liquidbase/voron-v0/docs/Input Shaping Graphs/beltscomparison_20240730_230938.png

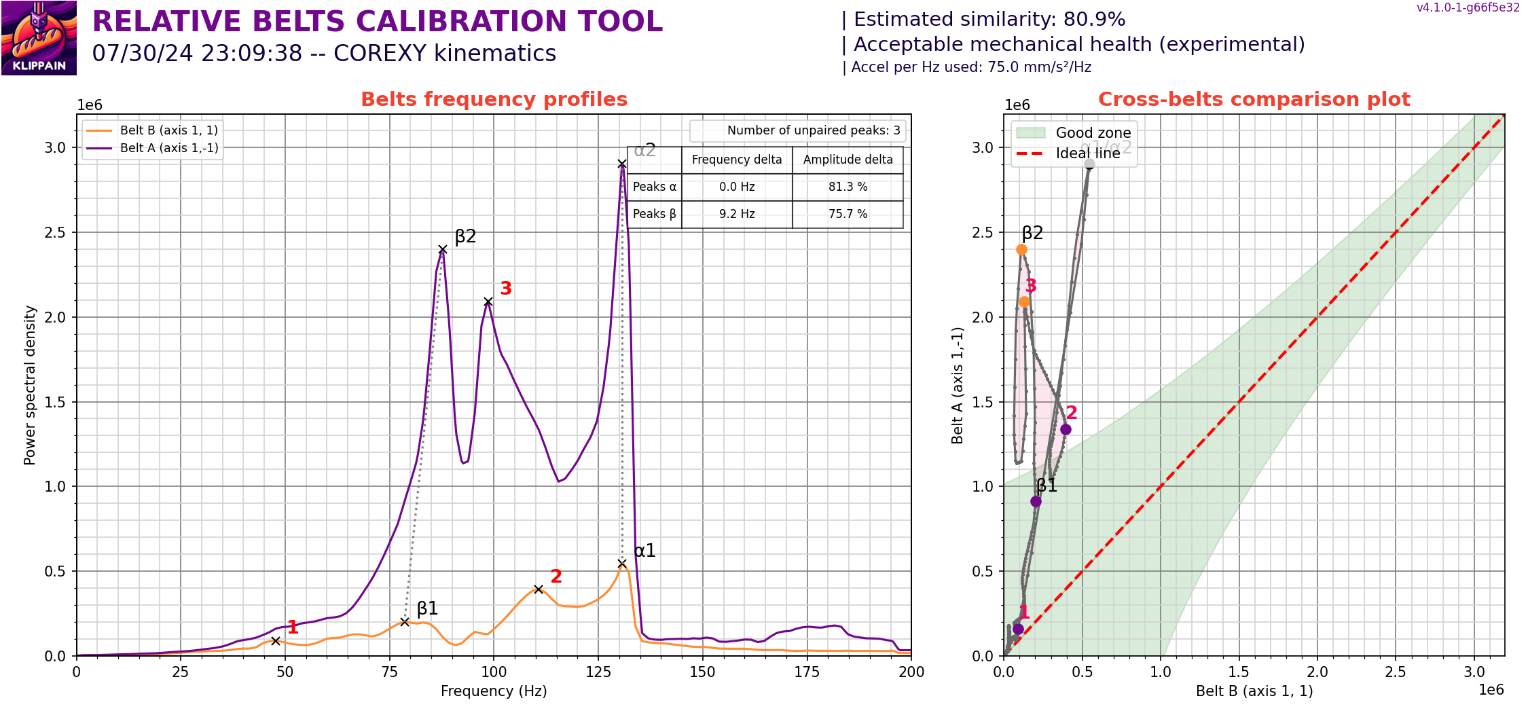
docs/Input Shaping Graphs/beltscomparison_20240730_230938.png
