liquidbase/voron-v0/docs/Input Shaping Graphs/inputshaper_20240730_230241_X.png

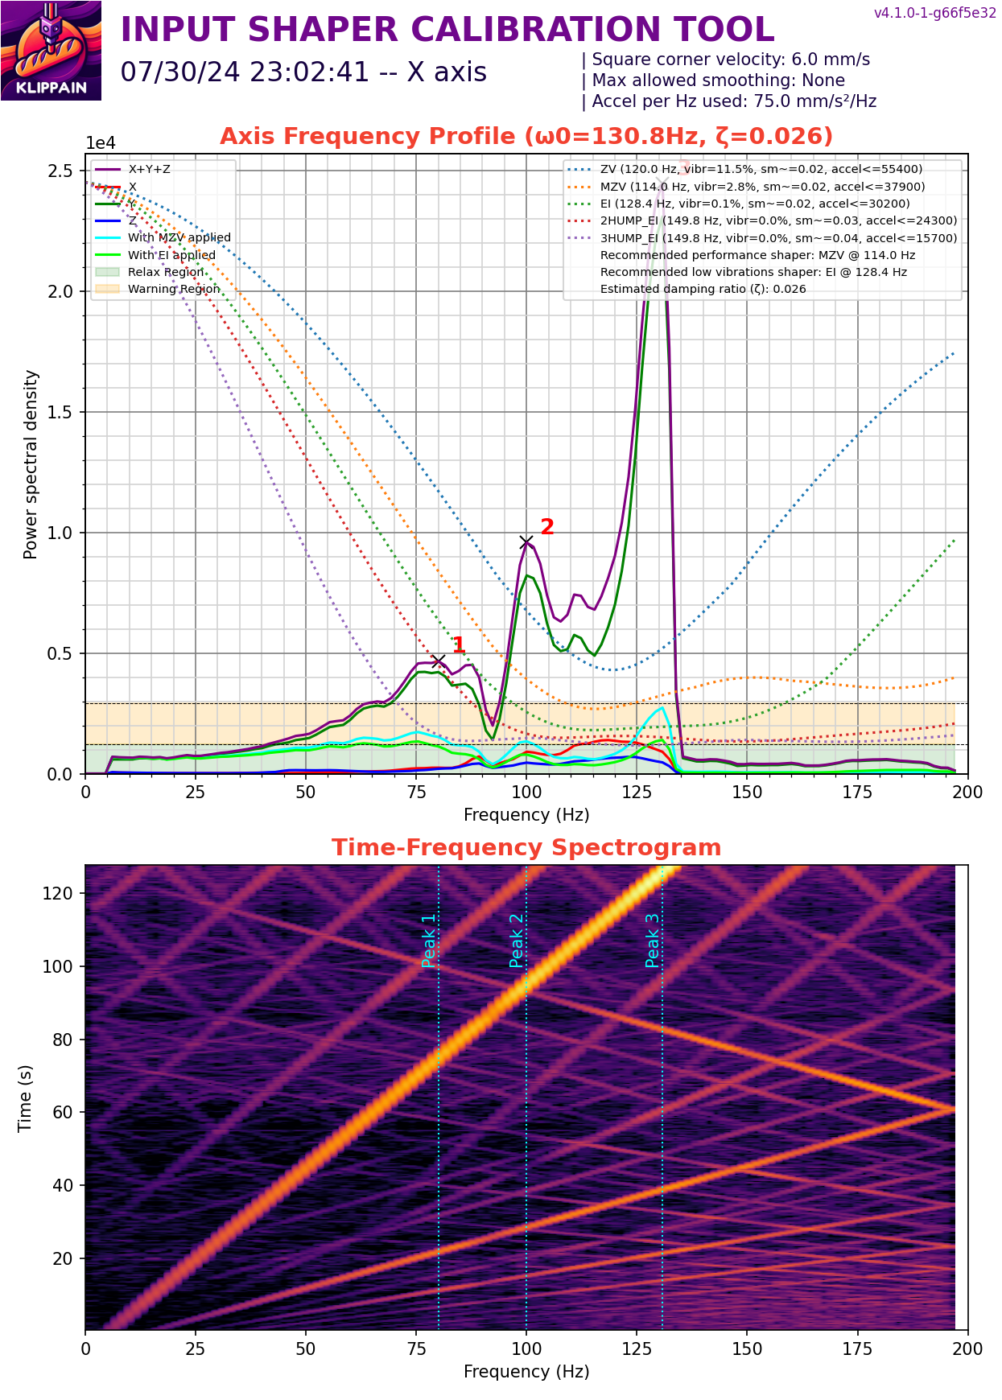
docs/Input Shaping Graphs/inputshaper_20240730_230241_X.png
