liquidbase/voron-v0/docs/Input Shaping Graphs/inputshaper_20240730_233401_Y.png

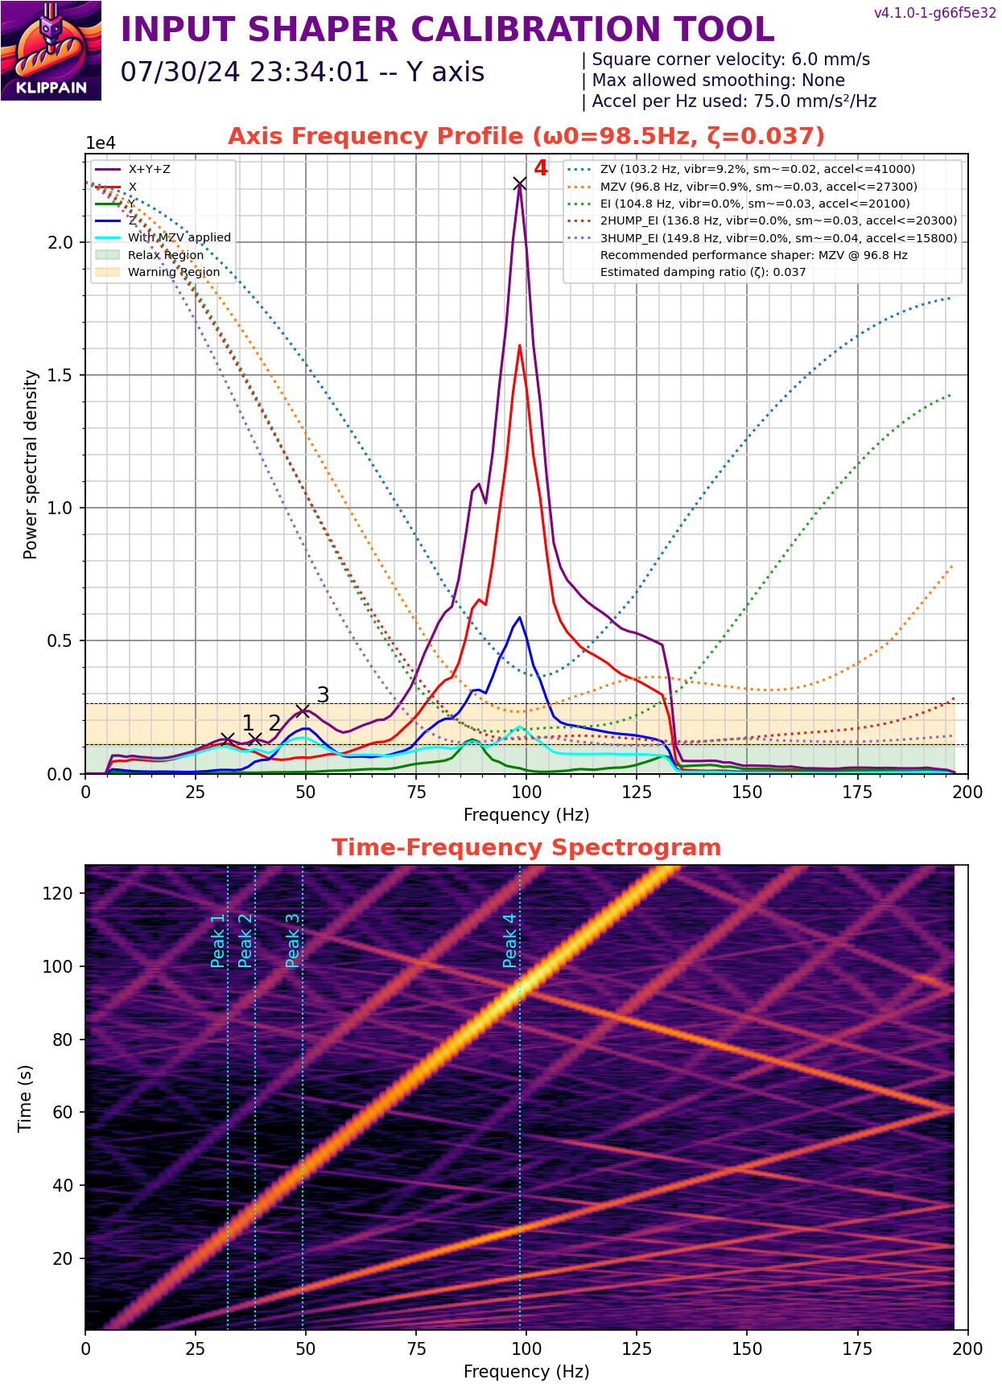
docs/Input Shaping Graphs/inputshaper_20240730_233401_Y.png
