liquidbase/voron-v0/Pictures/extruder_motor.jpg

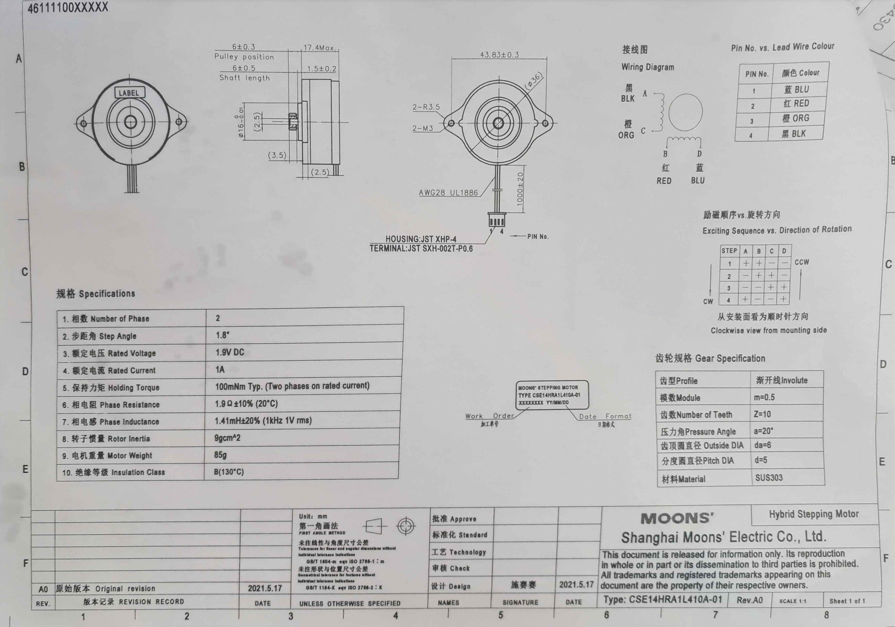
Pictures/extruder_motor.jpg
