liquidbase/voron-v0/Pictures/PXL_20240726_175340386.jpg

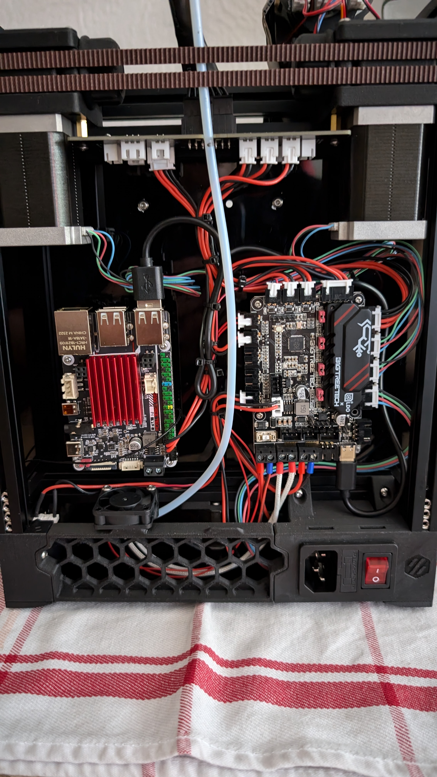
Pictures/PXL_20240726_175340386.jpg
