liquidbase/voron-v0/Pictures/xy_motor.jpg

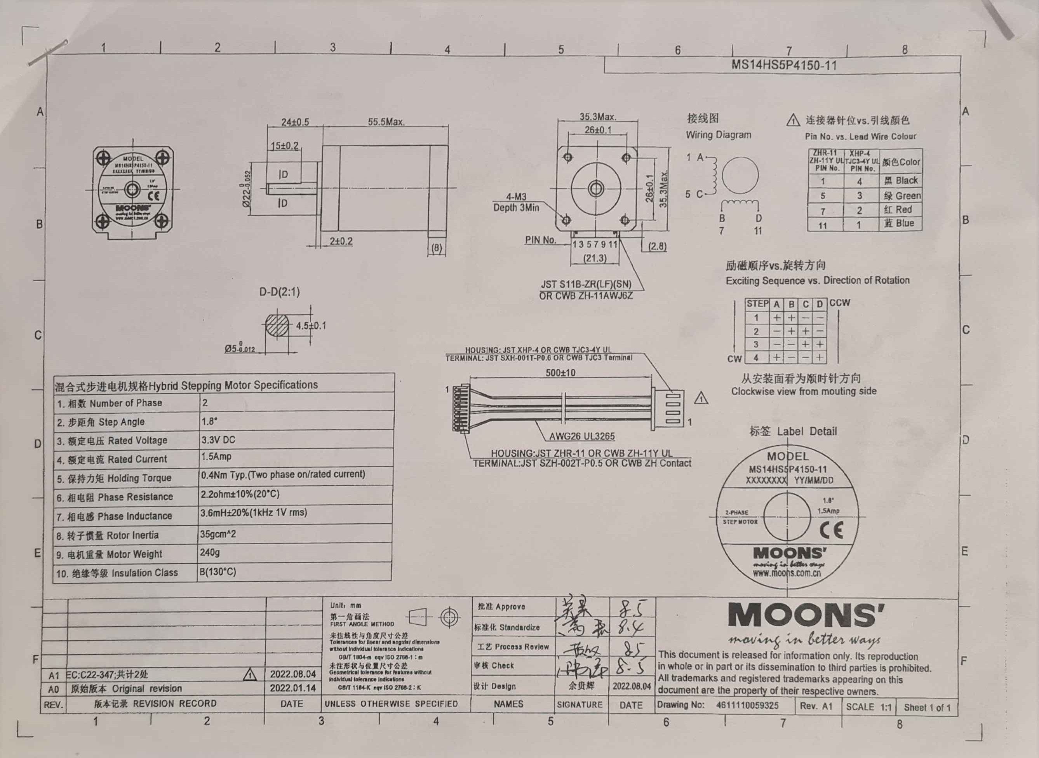
Pictures/xy_motor.jpg
