liquidbase/voron-v0/Pictures/z_motor.jpg

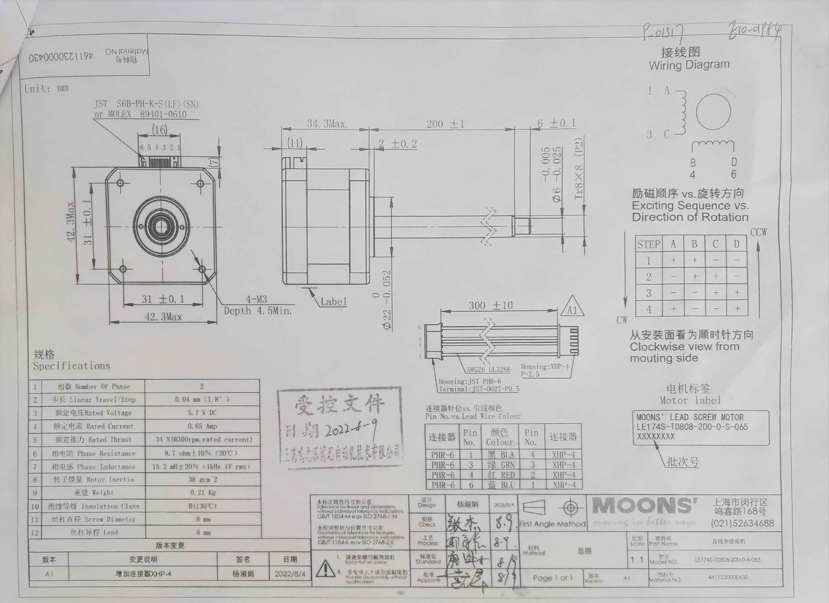
Pictures/z_motor.jpg
