liquidbase/voron-v0/Printfiles/voron-v0-stealth-handles/stealth_handle.step

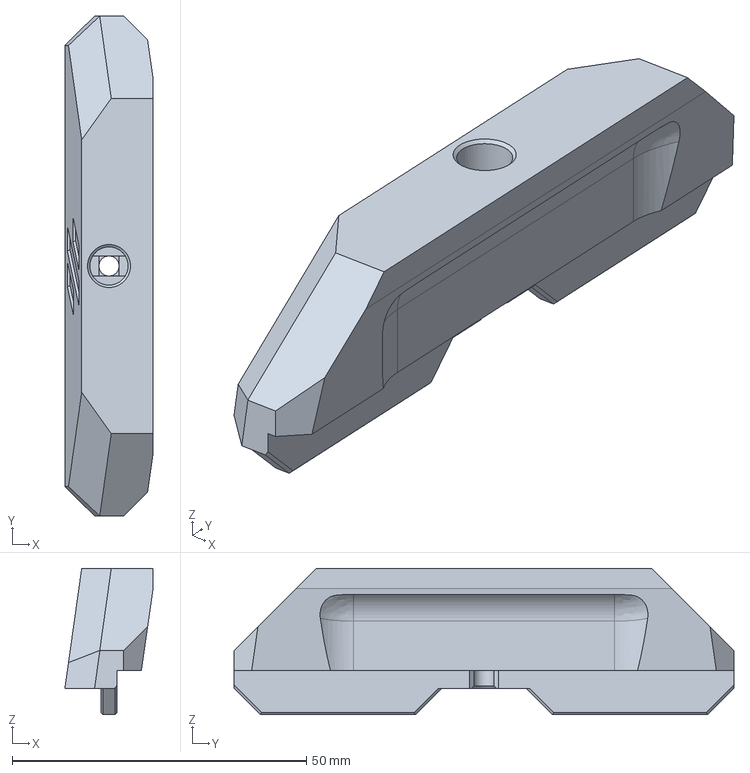
[picture p18: CAD file, 2024-07-29]
Printfiles/voron-v0-stealth-handles/stealth_handle.step
15.0 x 85.0 x 24.9 mm
