liquidbase/voron-v0/Printfiles/Sherpa_Mini-Extruder/Assembly_Tools/Shaft_Grinding_Tool/bottom.stl

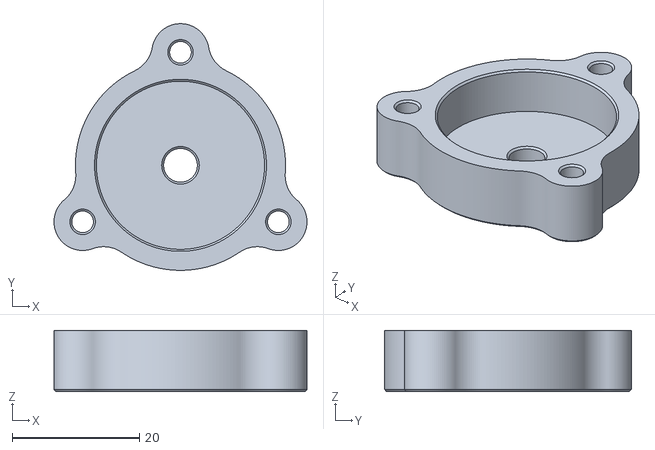
[picture p24: CAD file, 2024-10-22]
Printfiles/Sherpa_Mini-Extruder/Assembly_Tools/Shaft_Grinding_Tool/bottom.stl
39.7 x 38.7 x 9.60
