liquidbase/voron-v0/Printfiles/Sherpa_Mini-Extruder/STLs/housing_rear_x1_rev17.STL

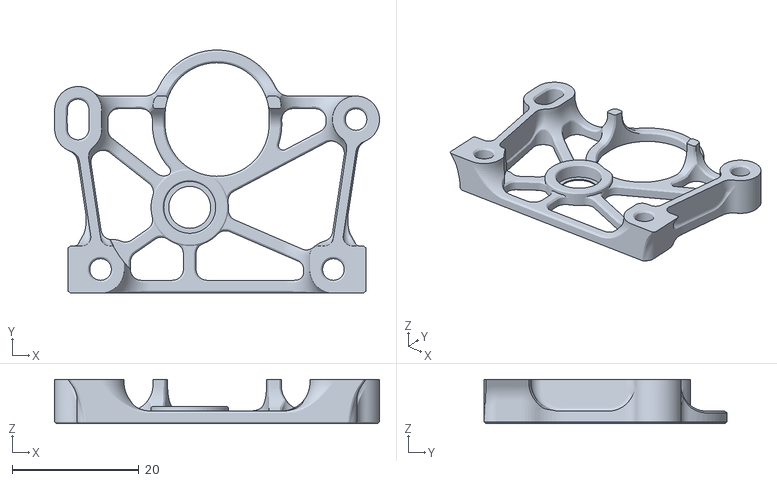
[picture p25: CAD file, 2024-10-22]
Printfiles/Sherpa_Mini-Extruder/STLs/housing_rear_x1_rev17.STL
51.2 x 38.3 x 7.00
