liquidbase/voron-v0/Printfiles/Sherpa_Mini-Extruder/STLs/optional_parts/[a]_housing_front_k_x1_rev15.STL

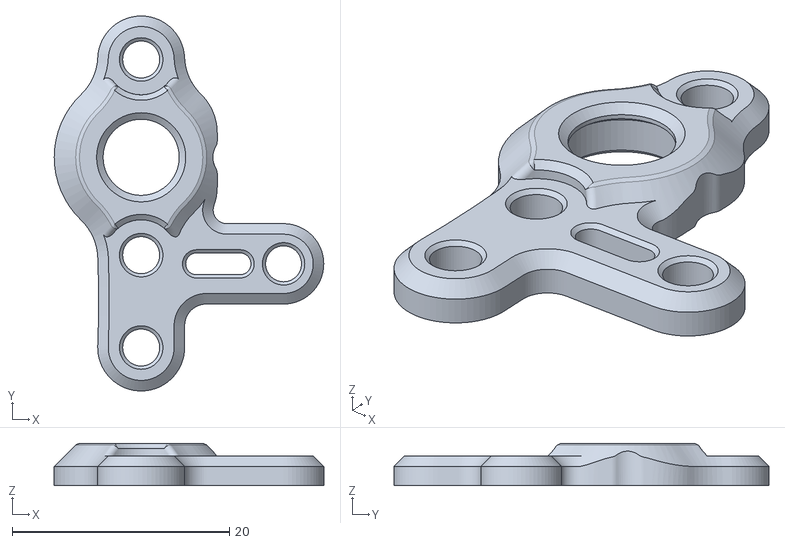
[picture p26: CAD file, 2024-10-22]
Printfiles/Sherpa_Mini-Extruder/STLs/optional_parts/[a]_housing_front_k_x1_rev15.STL
24.8 x 34.5 x 3.90
