liquidbase/voron-v0/Printfiles/voron-v0-stealth-handles/handle_a.stl

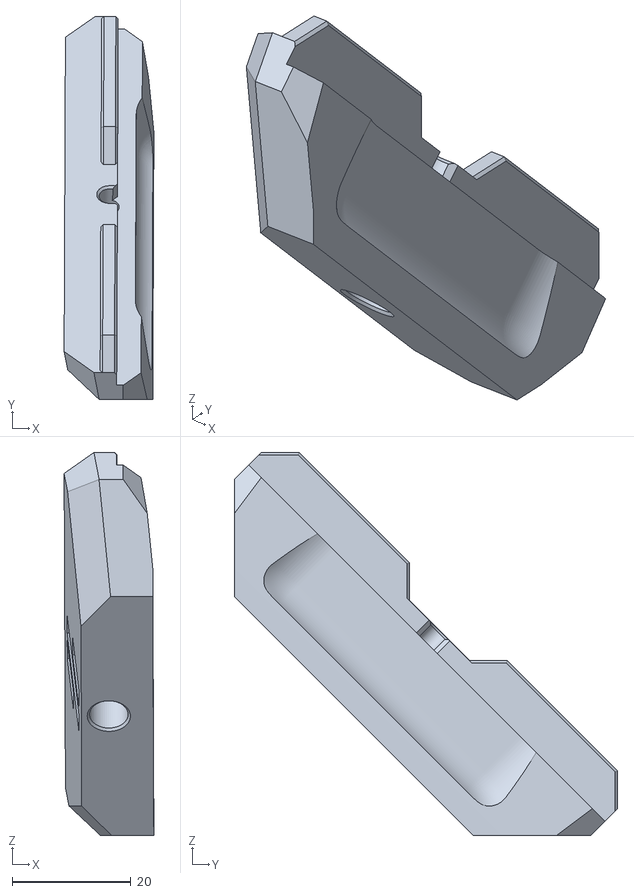
[picture p27: CAD file, 2024-07-29]
Printfiles/voron-v0-stealth-handles/handle_a.stl
15.2 x 64.7 x 64.6
