liquidbase/voron-v0/Printfiles/waveshare-43-inch-display-mount-for-the-voron-v01-model_files/vorn_v0_waveshare_43.3mf

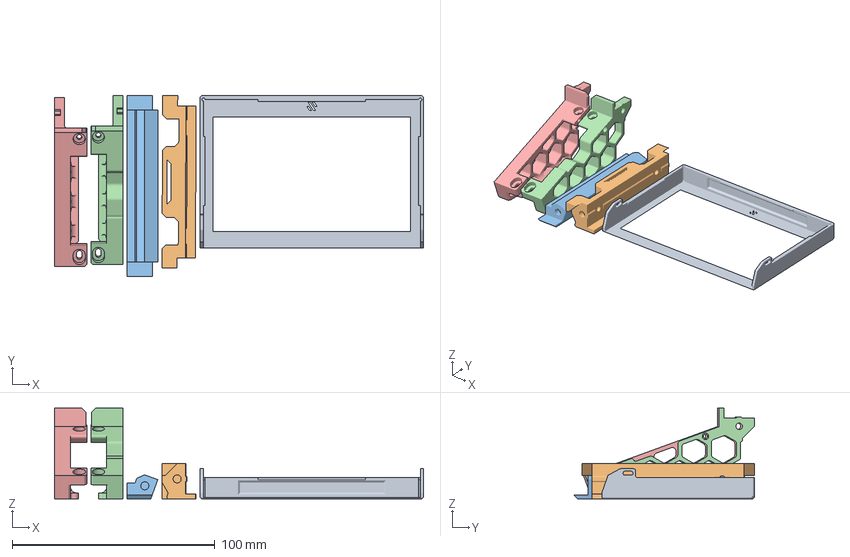
[picture p28: CAD file, 2024-08-06]
Printfiles/waveshare-43-inch-display-mount-for-the-voron-v01-model_files/vorn_v0_waveshare_43.3mf
181.8 x 89.1 x 44.8 mm
cover_front.stl
mount_rear.stl
mount_front.stl
mount_left.stl
mount_right.stl
