liquidbase/voron-v0/Printfiles/[a]_Foot_Accent_A_x2.stl

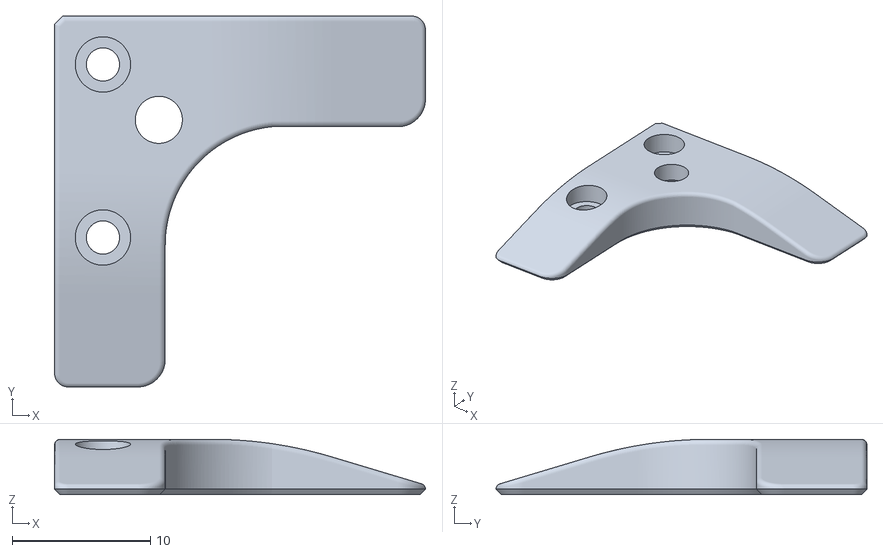
[picture p29: CAD file, 2024-11-05]
Printfiles/[a]_Foot_Accent_A_x2.stl
26.8 x 26.8 x 4.00
