liquidbase/voron-v0/Printfiles/Dragon_Burner_v8_Sherpa_Mini/Sherpa_Mini_Mount.stl

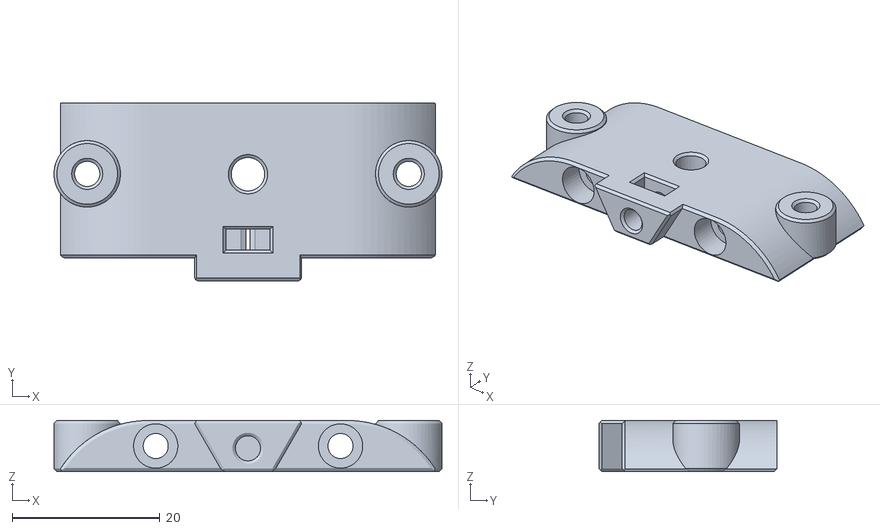
[picture p30: CAD file, 2024-09-15]
Printfiles/Dragon_Burner_v8_Sherpa_Mini/Sherpa_Mini_Mount.stl
52.5 x 24.1 x 6.90
