liquidbase/voron-v0/Printfiles/Endstop Case/1515 Endcap with Endstop Case v14.step

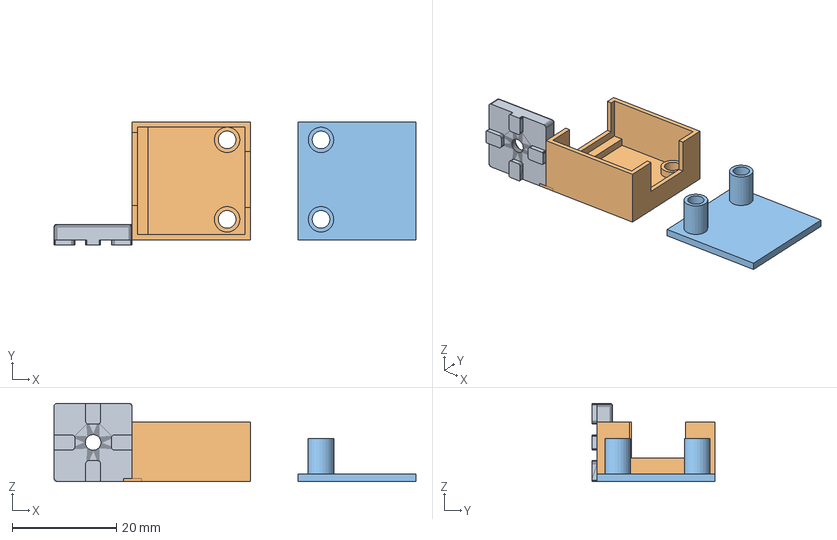
[picture p31: CAD file, 2024-09-08]
Printfiles/Endstop Case/1515 Endcap with Endstop Case v14.step
69.4 x 23.7 x 15.0 mm
