liquidbase/voron-v0/Printfiles/Filler 66mm Remix - 5335512/files/FillerRollerSource-66mm.stl

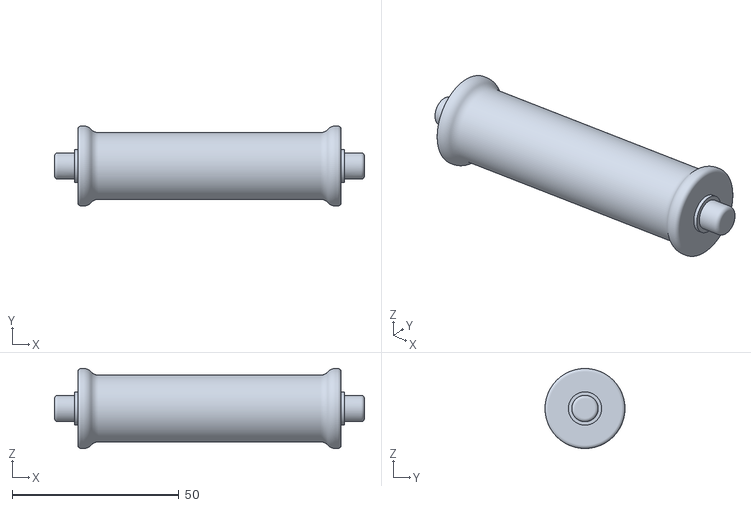
[picture p32: CAD file, 2024-10-22]
Printfiles/Filler 66mm Remix - 5335512/files/FillerRollerSource-66mm.stl
93.0 x 24.0 x 24.0
