liquidbase/voron-v0/Printfiles/Sherpa_Mini-Extruder/Assembly_Tools/Shaft_Grinding_Tool/top.stl

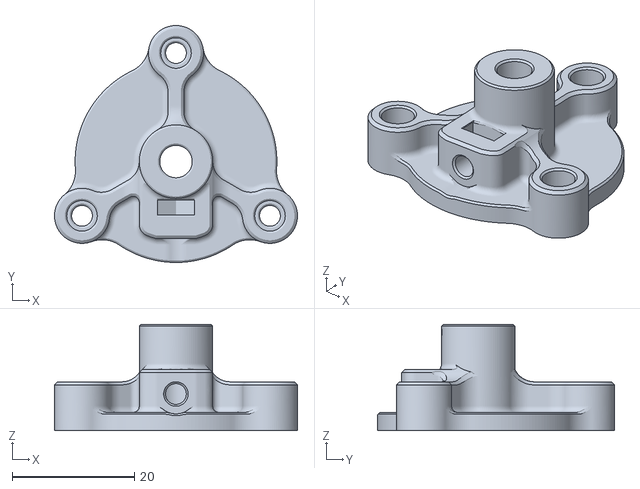
[picture p33: CAD file, 2024-10-22]
Printfiles/Sherpa_Mini-Extruder/Assembly_Tools/Shaft_Grinding_Tool/top.stl
39.7 x 38.8 x 17.4
