liquidbase/voron-v0/Printfiles/Sherpa_Mini-Extruder/STLs/[a]_idler_arm_long_x1_rev16a.STL

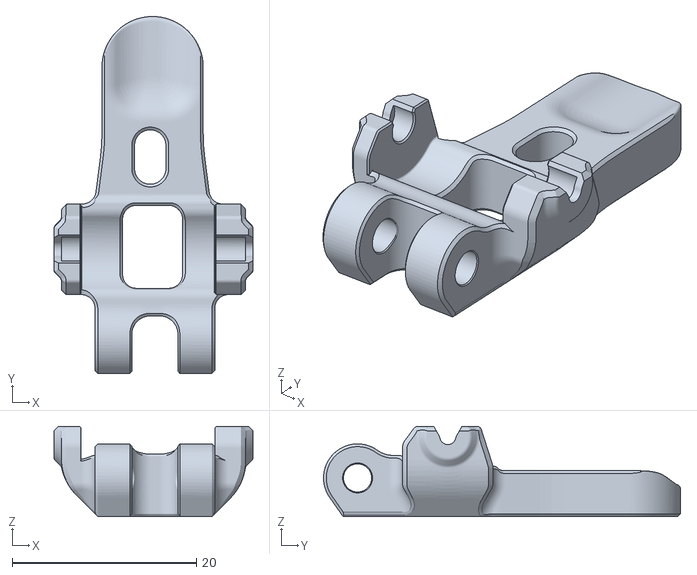
[picture p34: CAD file, 2024-10-22]
Printfiles/Sherpa_Mini-Extruder/STLs/[a]_idler_arm_long_x1_rev16a.STL
21.6 x 38.8 x 9.80
