liquidbase/voron-v0/Printfiles/Sherpa_Mini-Extruder/STLs/optional_parts/[a]_idler_arm_short_x1_rev16a.STL

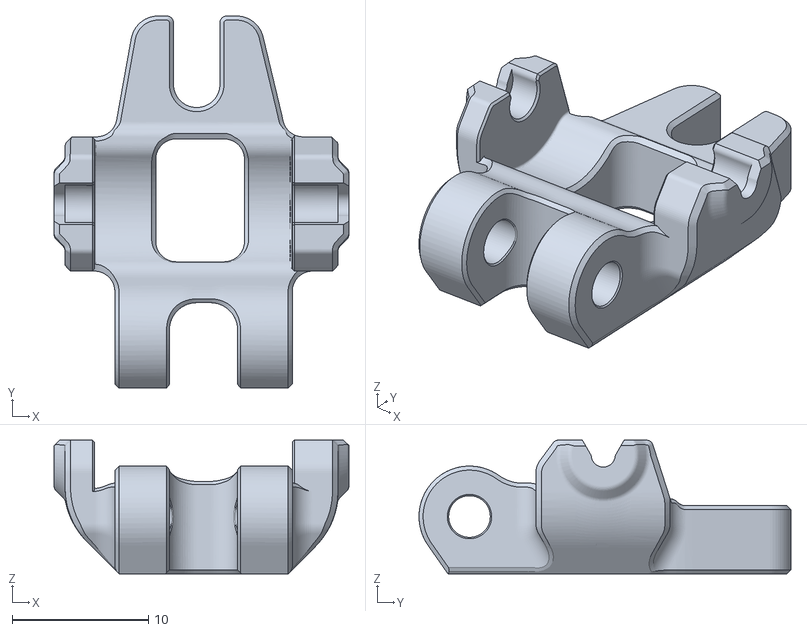
[picture p35: CAD file, 2024-10-22]
Printfiles/Sherpa_Mini-Extruder/STLs/optional_parts/[a]_idler_arm_short_x1_rev16a.STL
21.6 x 27.3 x 9.80
