liquidbase/voron-v0/Printfiles/voron-v0-stealth-handles/handle_b.stl

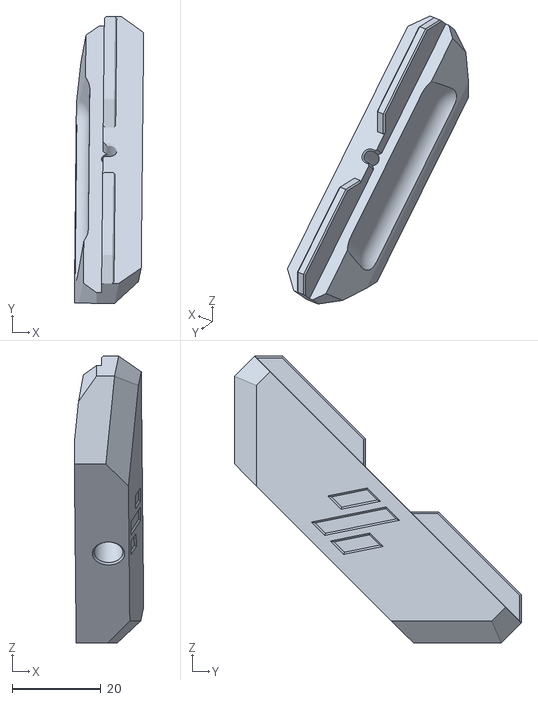
[picture p36: CAD file, 2024-07-29]
Printfiles/voron-v0-stealth-handles/handle_b.stl
15.6 x 64.7 x 64.6
