liquidbase/voron-v0/Printfiles/waveshare-43-inch-display-mount-for-the-voron-v01-model_files/cover_front.stl

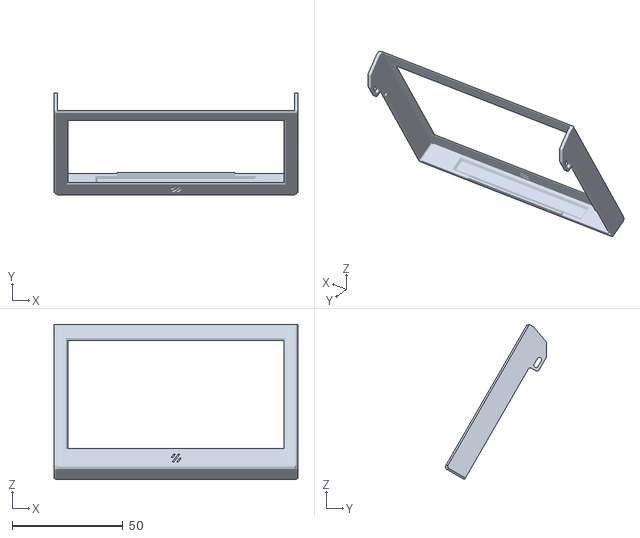
[picture p37: CAD file, 2024-08-06]
Printfiles/waveshare-43-inch-display-mount-for-the-voron-v01-model_files/cover_front.stl
110.0 x 45.8 x 70.0
