liquidbase/voron-v0/Printfiles/Dragon_Burner_v8_Sherpa_Mini/Cowl_ZeroClick.stl

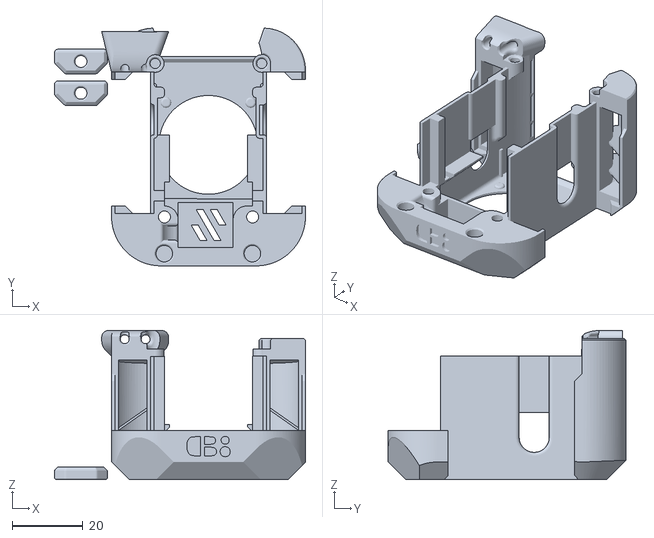
[picture p38: CAD file, 2024-09-14]
Printfiles/Dragon_Burner_v8_Sherpa_Mini/Cowl_ZeroClick.stl
71.2 x 67.4 x 42.4
