liquidbase/voron-v0/Printfiles/waveshare-43-inch-display-mount-for-the-voron-v01-model_files/mount_rear.stl

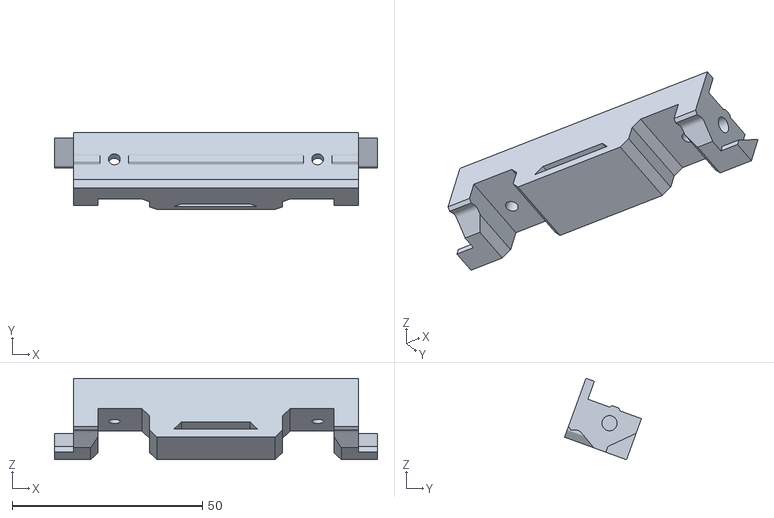
[picture p39: CAD file, 2024-08-06]
Printfiles/waveshare-43-inch-display-mount-for-the-voron-v01-model_files/mount_rear.stl
85.0 x 20.3 x 21.4
