liquidbase/voron-v0/Printfiles/Dragon_Burner_v8_Sherpa_Mini/Brace_Straight.stl

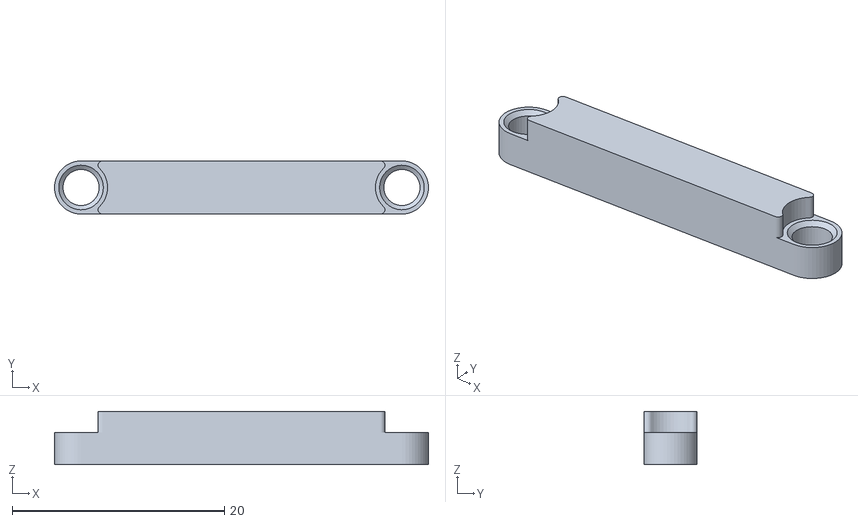
[picture p40: CAD file, 2024-09-14]
Printfiles/Dragon_Burner_v8_Sherpa_Mini/Brace_Straight.stl
35.2 x 5.00 x 5.00
