liquidbase/voron-v0/Printfiles/URBIFS-PC4.stl

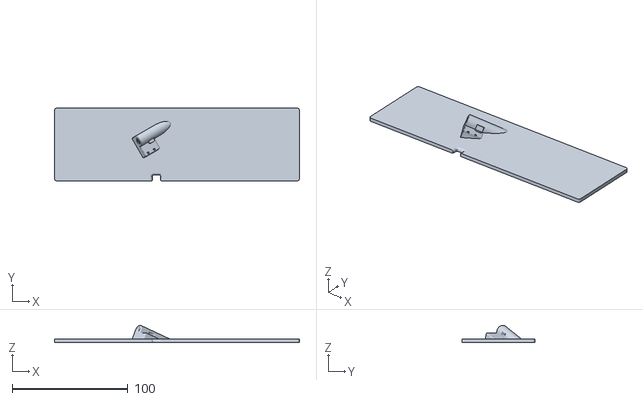
[picture p41: CAD file, 2024-10-27]
Printfiles/URBIFS-PC4.stl
212.0 x 63.0 x 15.0
