liquidbase/voron-v0/Printfiles/waveshare-43-inch-display-mount-for-the-voron-v01-model_files/mount_right.stl

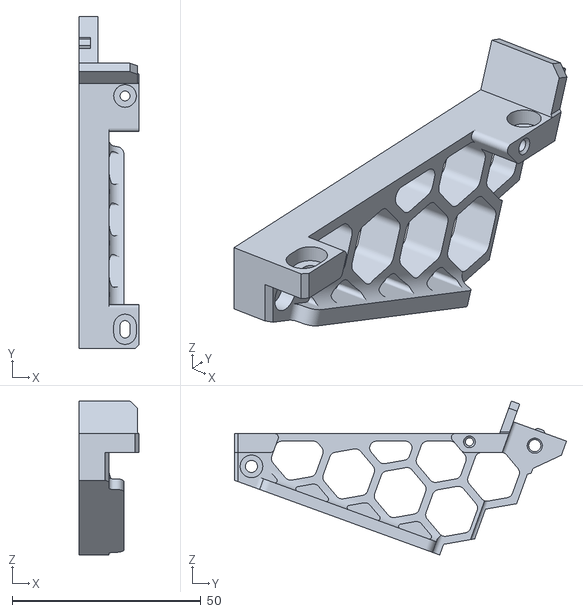
[picture p42: CAD file, 2024-08-06]
Printfiles/waveshare-43-inch-display-mount-for-the-voron-v01-model_files/mount_right.stl
15.9 x 88.0 x 40.8
