liquidbase/voron-v0/Printfiles/Dragon_Burner_v8_Sherpa_Mini/[c]_Voron_Diffuser.stl

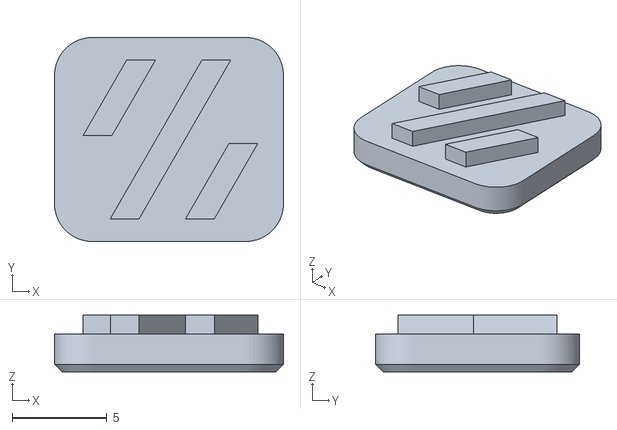
[picture p43: CAD file, 2024-09-14]
Printfiles/Dragon_Burner_v8_Sherpa_Mini/[c]_Voron_Diffuser.stl
12.1 x 10.7 x 3.00
