liquidbase/voron-v0/Printfiles/v0_chamber_thermistor_mount.stl

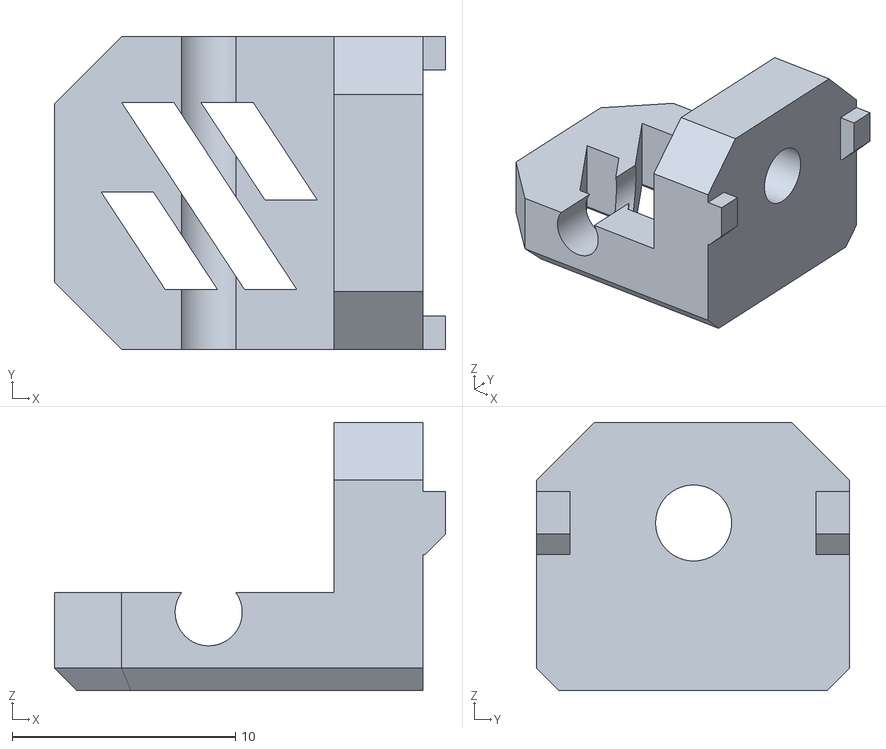
[picture p44: CAD file, 2024-10-26]
Printfiles/v0_chamber_thermistor_mount.stl
17.5 x 14.0 x 12.0
