liquidbase/voron-v0/Printfiles/waveshare-43-inch-display-mount-for-the-voron-v01-model_files/mount_front.stl

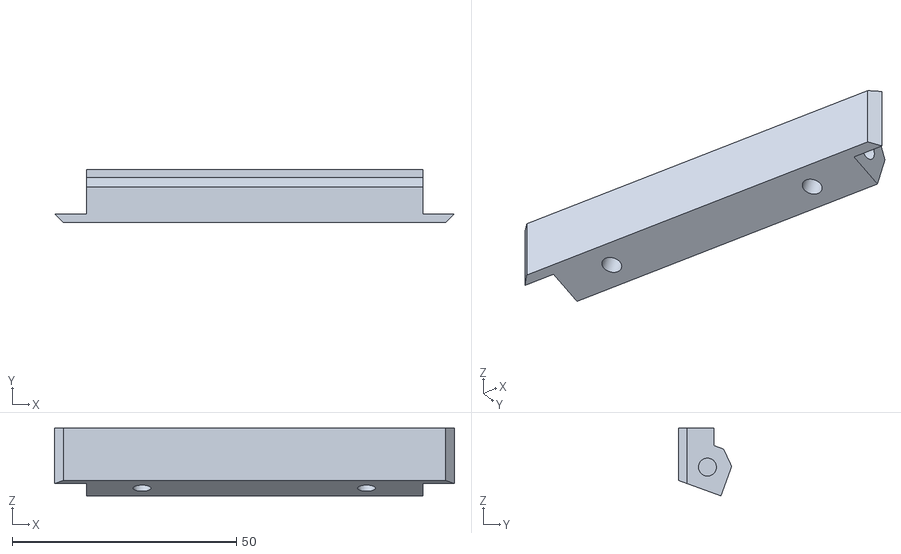
[picture p45: CAD file, 2024-08-06]
Printfiles/waveshare-43-inch-display-mount-for-the-voron-v01-model_files/mount_front.stl
89.1 x 11.9 x 15.1
