liquidbase/voron-v0/Printfiles/1515 End Cap with Y Endstop for Voron V0.stl

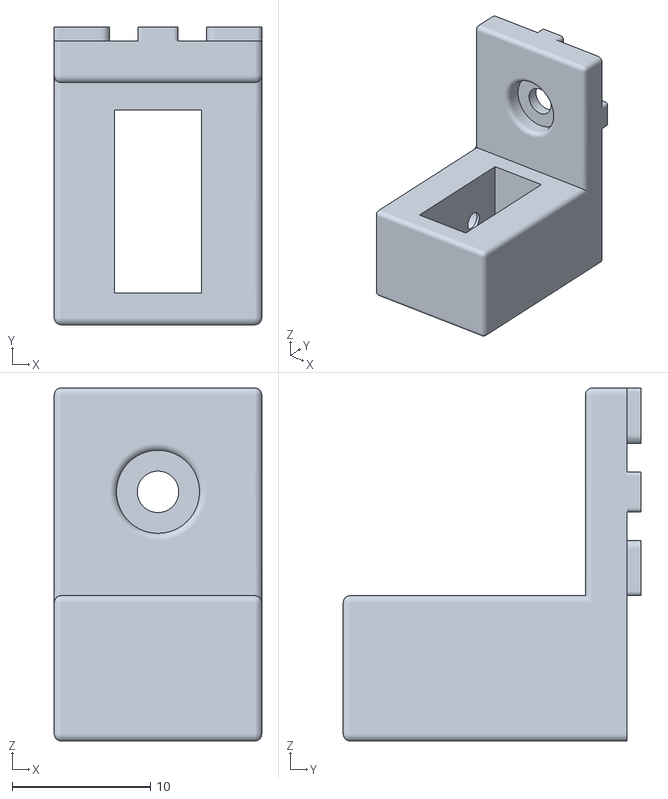
[picture p46: CAD file, 2024-10-26]
Printfiles/1515 End Cap with Y Endstop for Voron V0.stl
15.0 x 21.5 x 25.5
