liquidbase/voron-v0/Printfiles/x endstop.stl

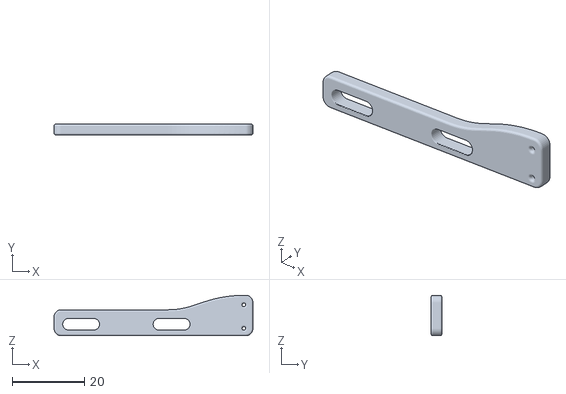
[picture p47: CAD file, 2024-10-26]
Printfiles/x endstop.stl
55.0 x 3.00 x 11.2
