liquidbase/voron-v0/Printfiles/1515_Hygrometer_mount.stl

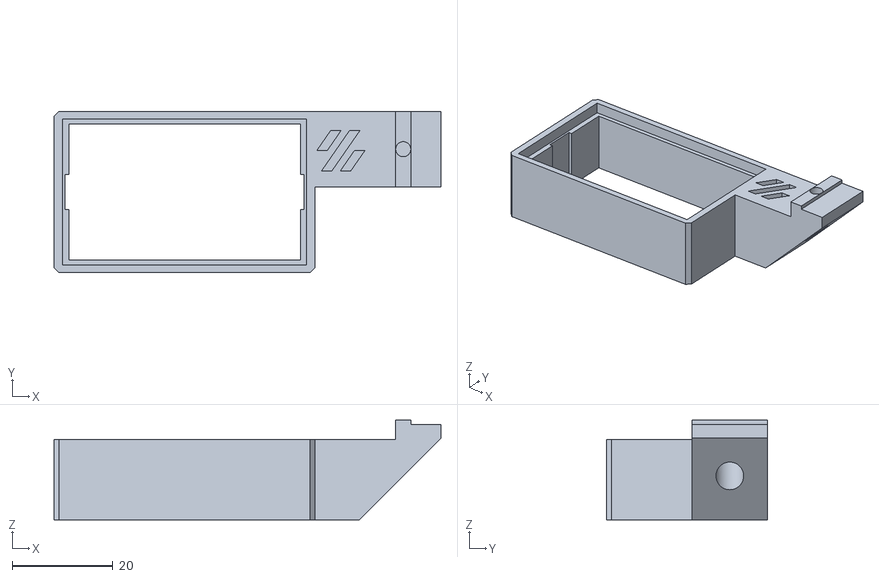
[picture p48: CAD file, 2024-10-22]
Printfiles/1515_Hygrometer_mount.stl
76.9 x 32.0 x 19.8
