liquidbase/voron-v0/Printfiles/URBI.stl

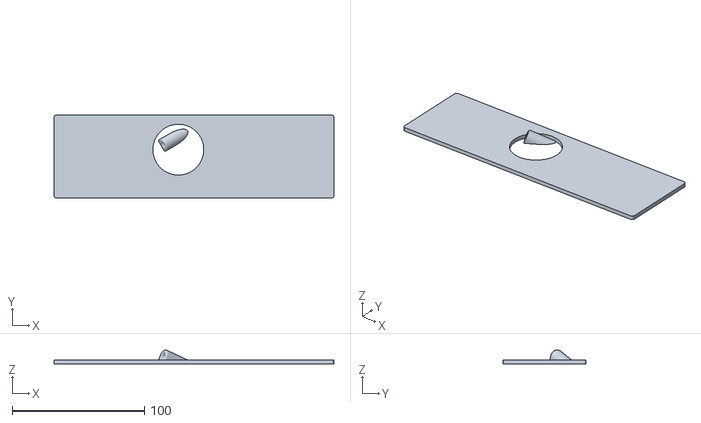
[picture p49: CAD file, 2024-10-22]
Printfiles/URBI.stl
212.0 x 63.0 x 10.7
