liquidbase/voron-v0/Printfiles/Door_Latch_x2.STL

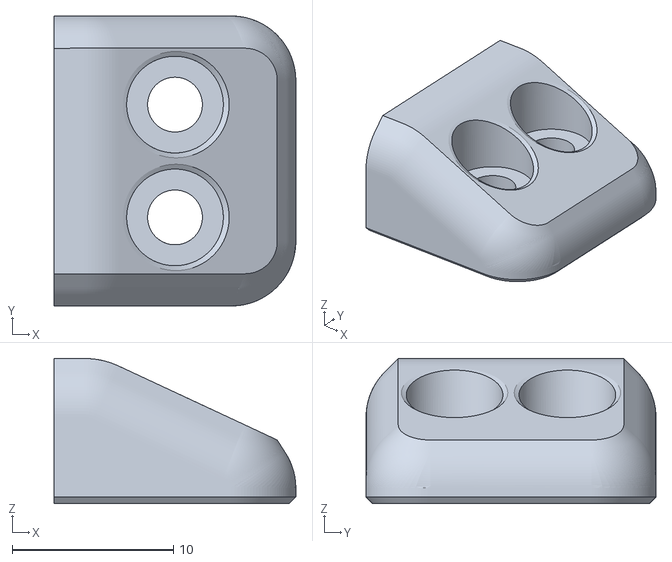
[picture p50: CAD file, 2024-10-22]
Printfiles/Door_Latch_x2.STL
15.0 x 18.0 x 9.00
