liquidbase/voron-v0/Printfiles/filler_brace_voron.stl

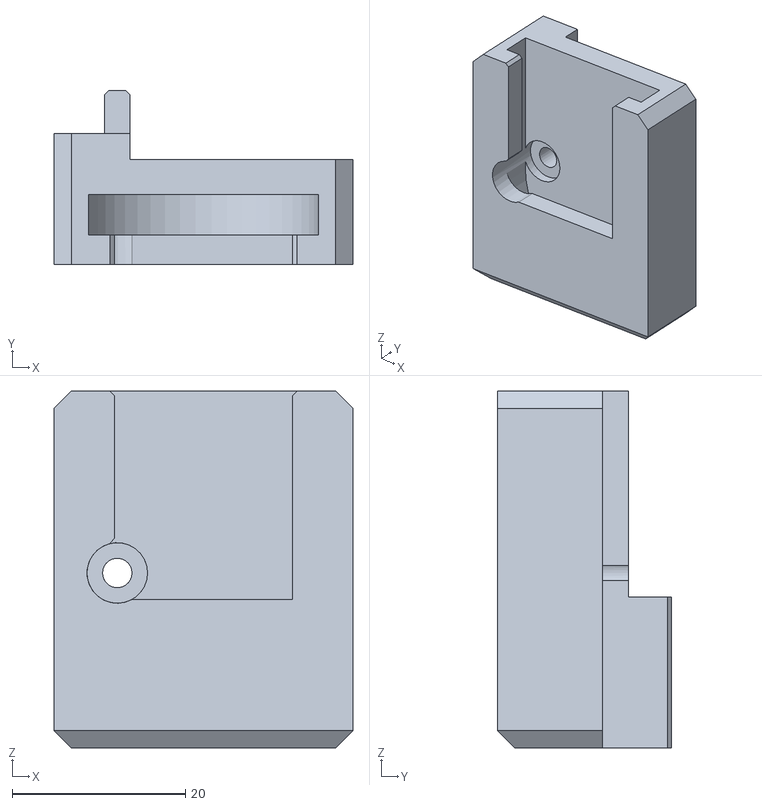
[picture p51: CAD file, 2024-10-22]
Printfiles/filler_brace_voron.stl
34.5 x 20.1 x 41.2
