liquidbase/voron-v0/Printfiles/Foot_Rear_Right_Plain.STL

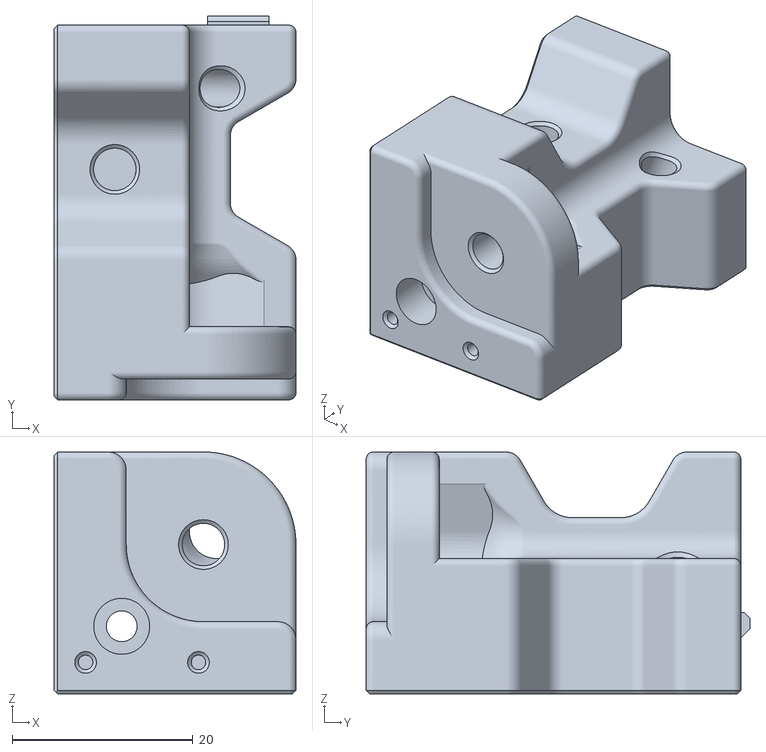
[picture p52: CAD file, 2024-10-22]
Printfiles/Foot_Rear_Right_Plain.STL
26.8 x 42.5 x 26.8
