liquidbase/voron-v0/Printfiles/V0 Bed Clip.stl

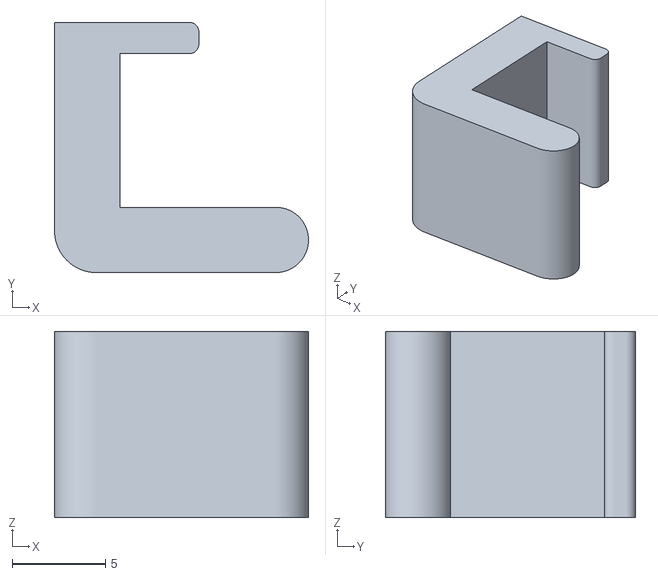
[picture p53: CAD file, 2024-10-22]
Printfiles/V0 Bed Clip.stl
13.6 x 13.4 x 10.0
