liquidbase/voron-v0/Printfiles/FillerWallMountSource v1.stl

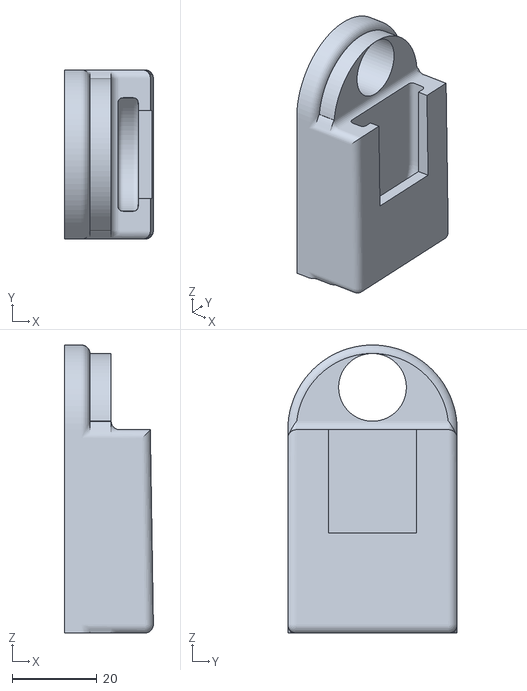
[picture p54: CAD file, 2024-10-22]
Printfiles/FillerWallMountSource v1.stl
21.0 x 40.0 x 68.0
