liquidbase/voron-v0/Printfiles/Right_Bottom_Front_Hinge_x1.stl

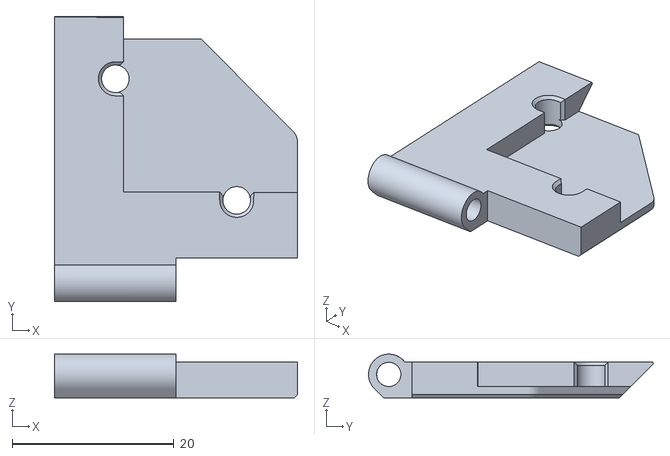
[picture p55: CAD file, 2024-09-07]
Printfiles/Right_Bottom_Front_Hinge_x1.stl
30.0 x 35.2 x 5.40
