liquidbase/voron-v0/Printfiles/Right_Top_Left_Hinge_x1.stl

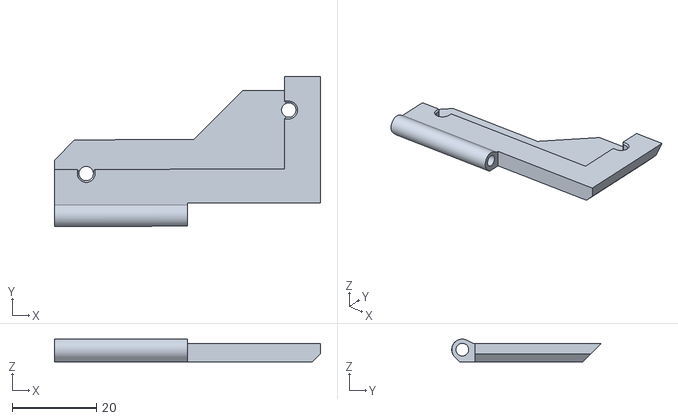
[picture p56: CAD file, 2024-09-07]
Printfiles/Right_Top_Left_Hinge_x1.stl
63.0 x 35.5 x 5.40
