liquidbase/voron-v0/Printfiles/Front_Top_Right_Hinge_x1.stl

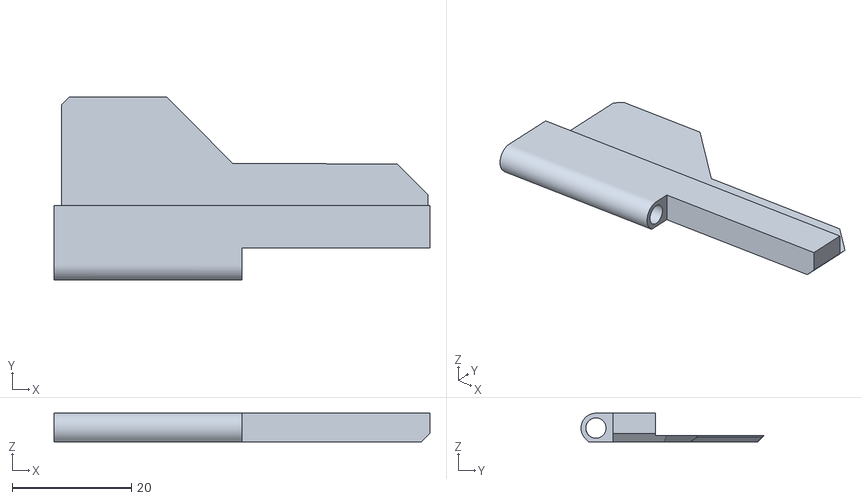
[picture p57: CAD file, 2024-08-15]
Printfiles/Front_Top_Right_Hinge_x1.stl
63.0 x 30.7 x 4.80
