liquidbase/voron-v0/Printfiles/voron v0 daylight diffuser v10.3mf

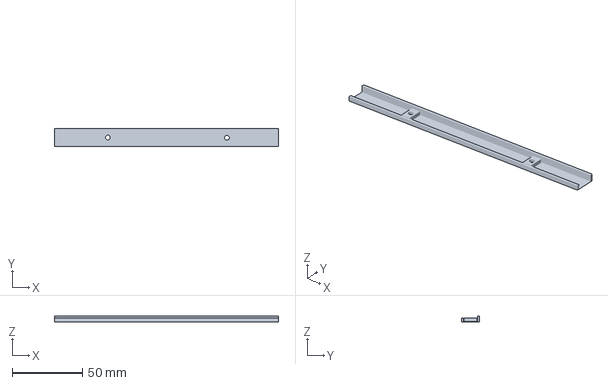
[picture p58: CAD file, 2024-08-15]
Printfiles/voron v0 daylight diffuser v10.3mf
160.0 x 13.0 x 4.40 mm
