liquidbase/voron-v0/Printfiles/Front_Bottom_Right_Hinge_x1.stl

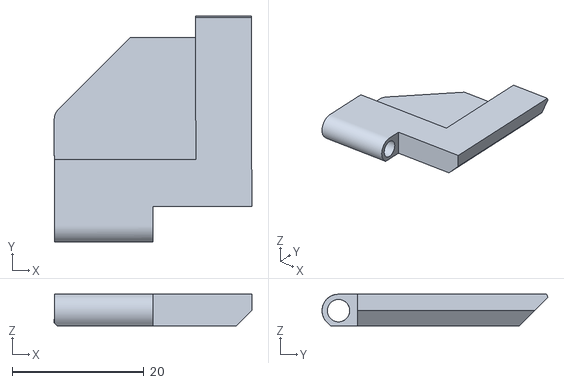
[picture p59: CAD file, 2024-08-07]
Printfiles/Front_Bottom_Right_Hinge_x1.stl
30.0 x 34.3 x 4.80
