liquidbase/voron-v0/Printfiles/Brackets_1515_x2.stl

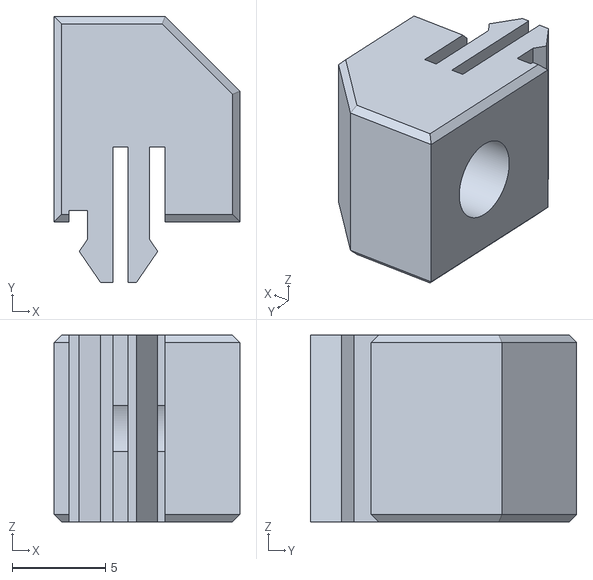
[picture p60: CAD file, 2024-08-07]
Printfiles/Brackets_1515_x2.stl
9.95 x 14.2 x 10.0
