liquidbase/voron-v0/Printfiles/V0.2_NTC_10k_B3950_Mount.stl

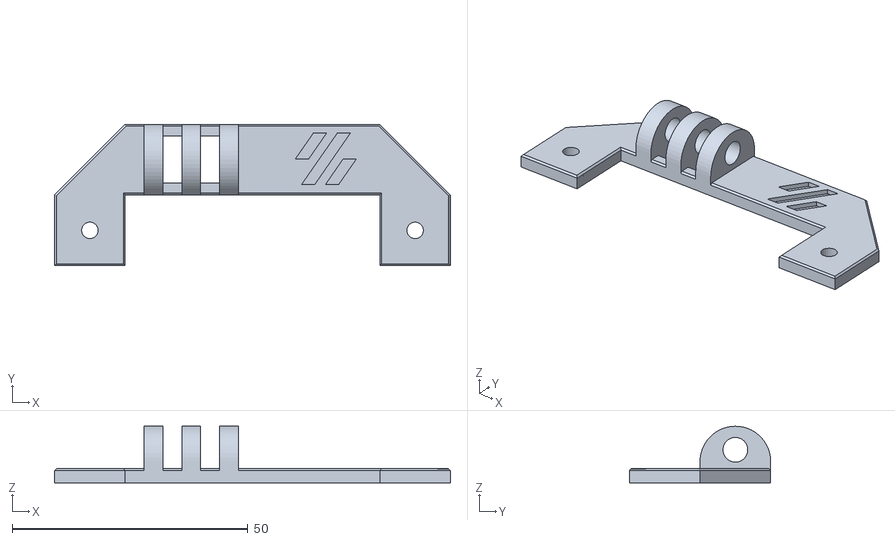
[picture p61: CAD file, 2024-08-04]
Printfiles/V0.2_NTC_10k_B3950_Mount.stl
84.0 x 30.0 x 12.0
