liquidbase/voron-v0/Printfiles/Voron_Design_Cube_v7.stl

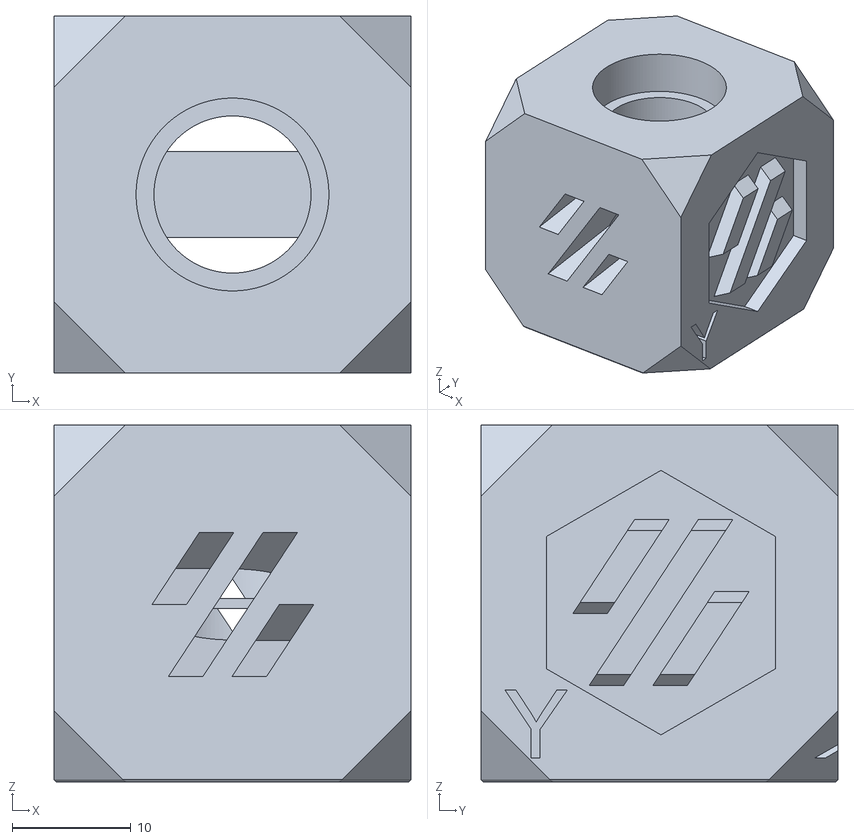
[picture p62: CAD file, 2024-07-28]
Printfiles/Voron_Design_Cube_v7.stl
30.0 x 30.0 x 30.0
