liquidbase/voron-v0/Printfiles/rear_panel.3mf

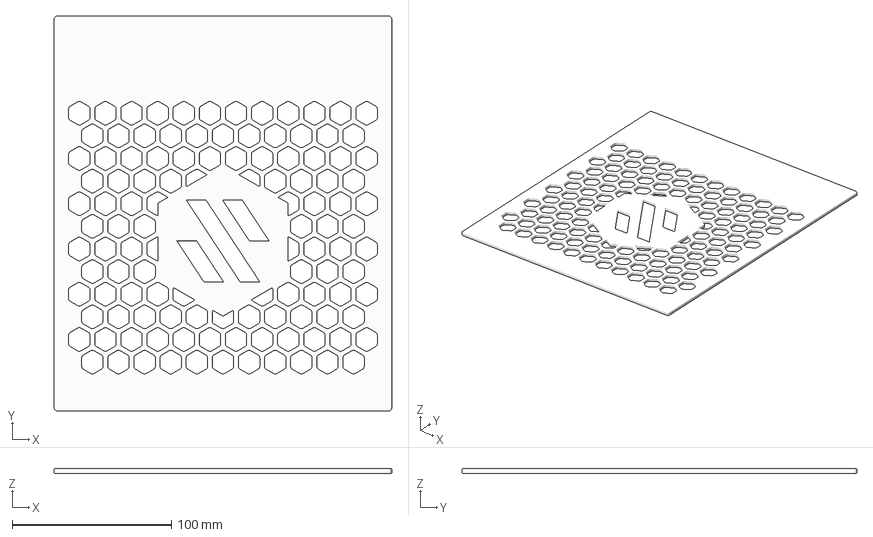
[picture p63: CAD file, 2024-07-27]
Printfiles/rear_panel.3mf
212.0 x 248.0 x 3.00 mm
