liquidbase/voron-v0/Printfiles/[a]_display_cover_hex_logo_x1.stl

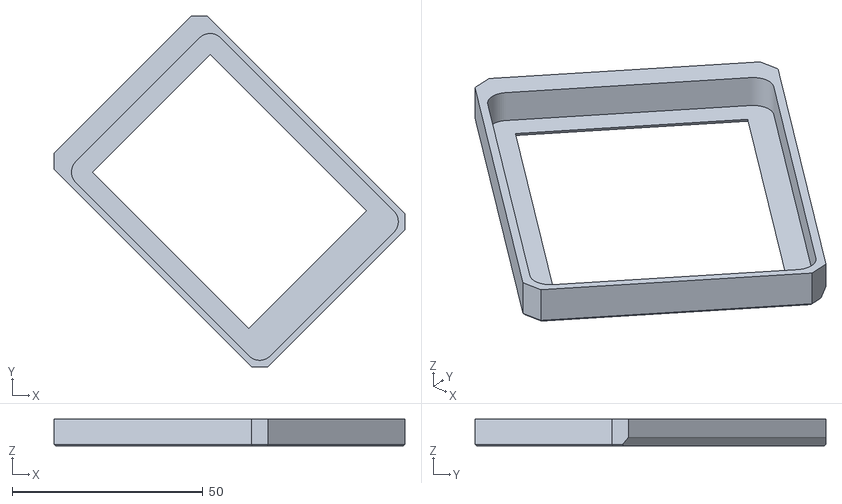
[picture p64: CAD file, 2024-07-26]
Printfiles/[a]_display_cover_hex_logo_x1.stl
92.1 x 92.1 x 7.00
