liquidbase/voron-v0/Printfiles/display_mount.stl

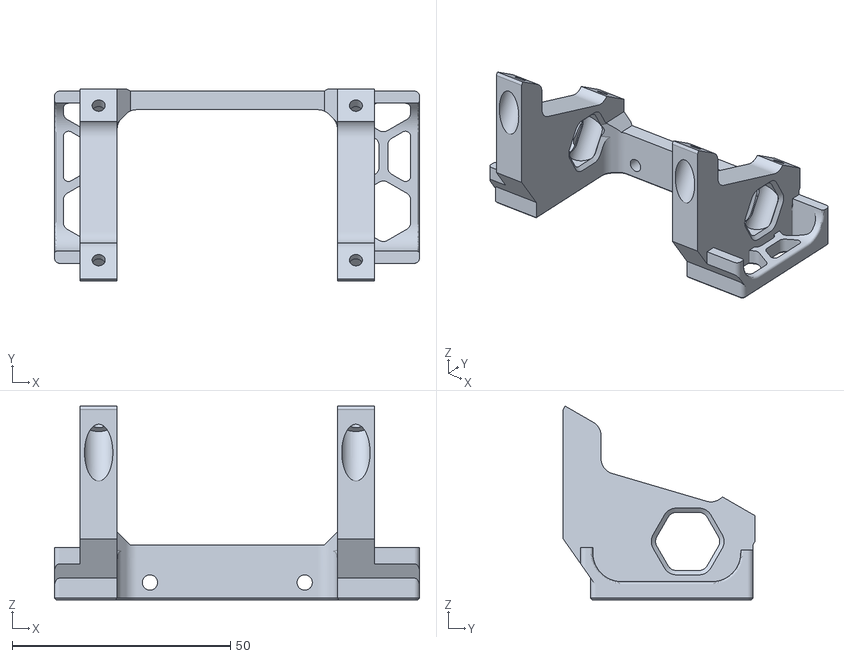
[picture p65: CAD file, 2024-07-26]
Printfiles/display_mount.stl
83.7 x 43.9 x 44.5
