liquidbase/voron-v0/Printfiles/RPi_or_BTT-Pico_Mount.STL

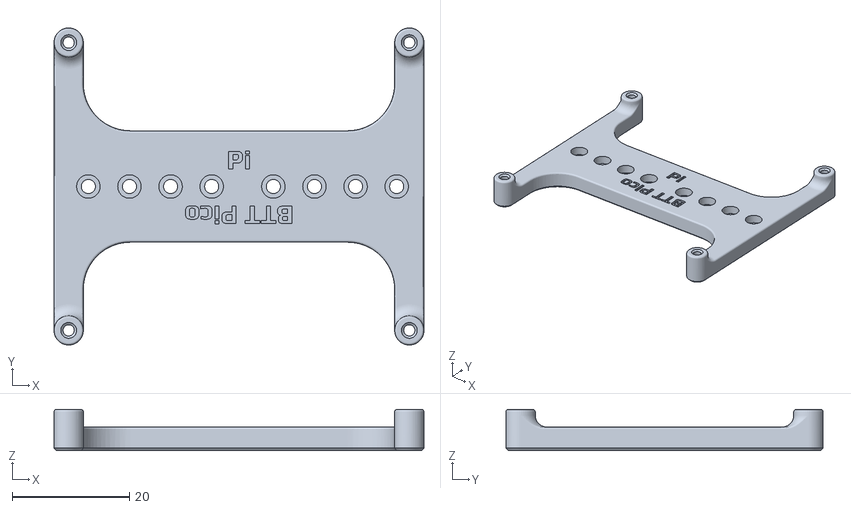
[picture p66: CAD file, 2024-07-26]
Printfiles/RPi_or_BTT-Pico_Mount.STL
63.0 x 54.0 x 7.00
