liquidbase/voron-v0/Printfiles/Filler 66mm Remix - 5335512/images/FillerBaseSource-66mm.png

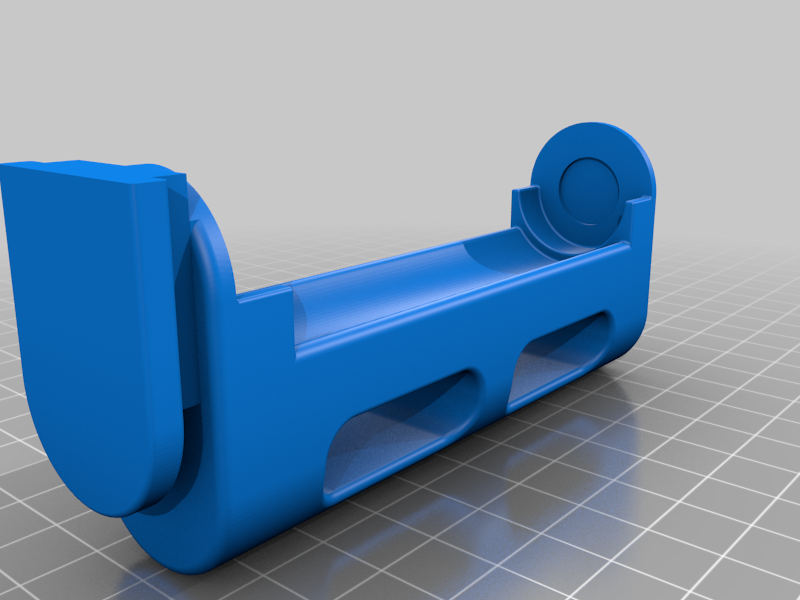
Printfiles/Filler 66mm Remix - 5335512/images/FillerBaseSource-66mm.png
