liquidbase/voron-v0/Printfiles/Sherpa_Mini-Extruder/Assembly_Tools/Shaft_Grinding_Tool/tool_1.png

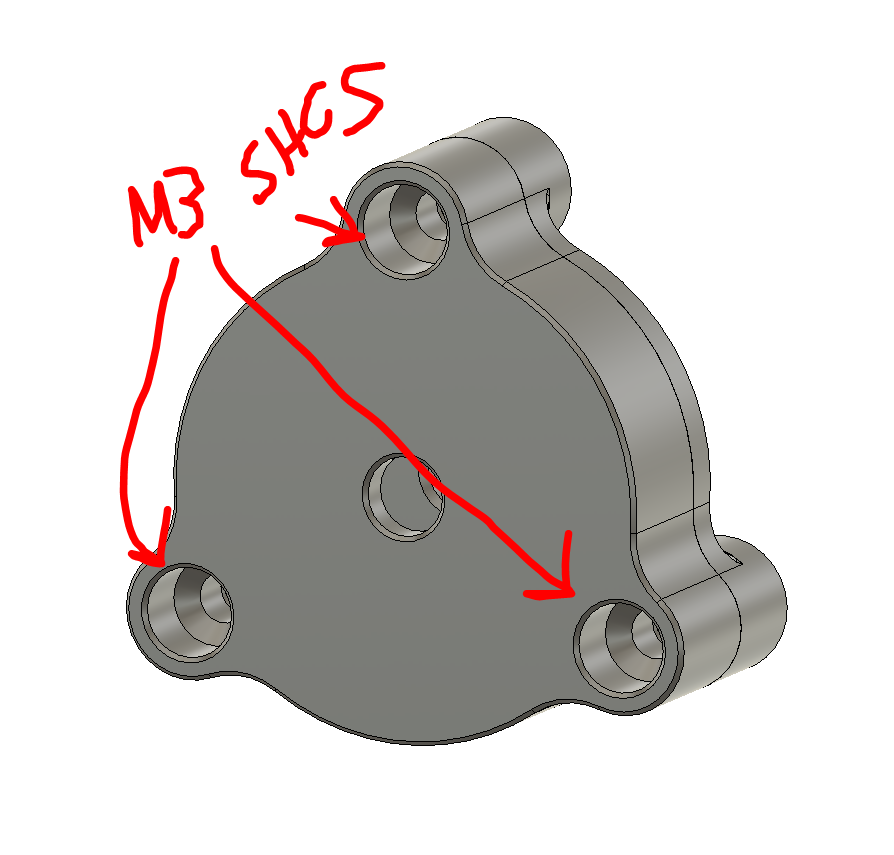
Printfiles/Sherpa_Mini-Extruder/Assembly_Tools/Shaft_Grinding_Tool/tool_1.png
